manjarimeedeniya/Team_Morpheus/Enclosure Files/Photos/Bottom_2 from SolidWorks.png

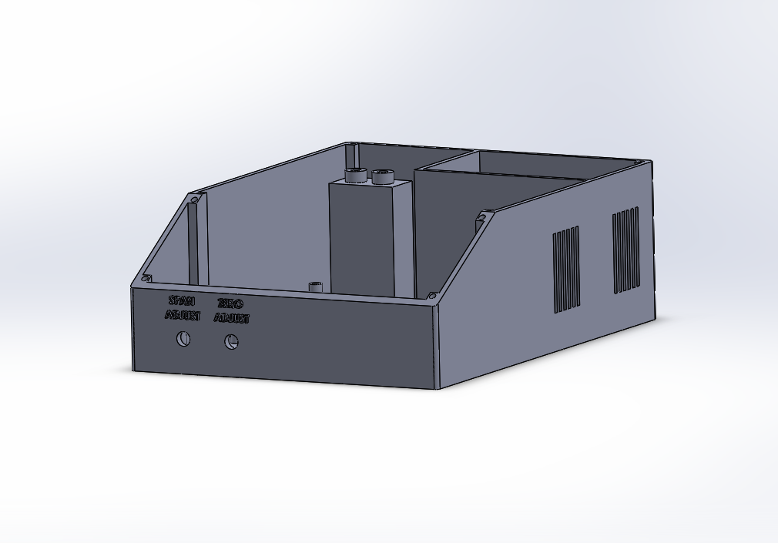
Enclosure Files/Photos/Bottom_2 from SolidWorks.png
