manjarimeedeniya/Team_Morpheus/Enclosure Files/Photos/Bottom_3 from SolidWorks.png

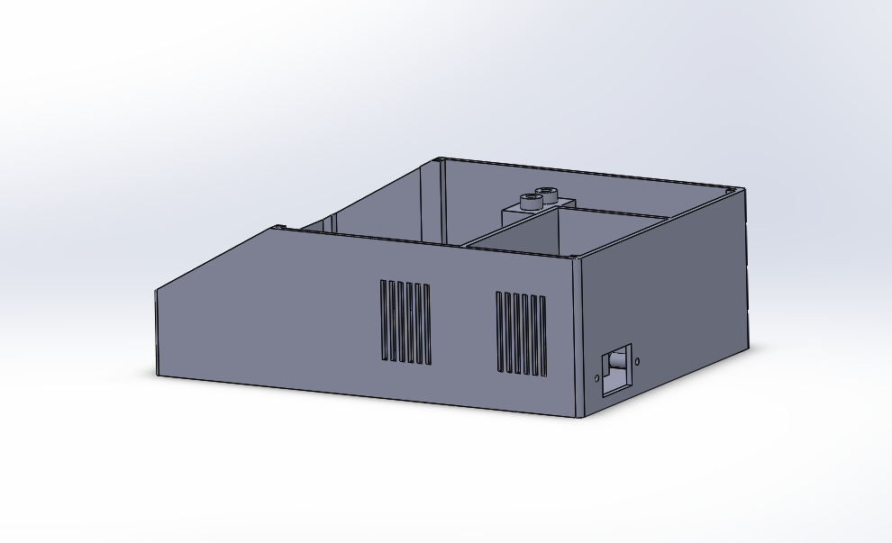
Enclosure Files/Photos/Bottom_3 from SolidWorks.png
