manjarimeedeniya/Team_Morpheus/Enclosure Files/Photos/Bottom_4 from SolidWorks.png

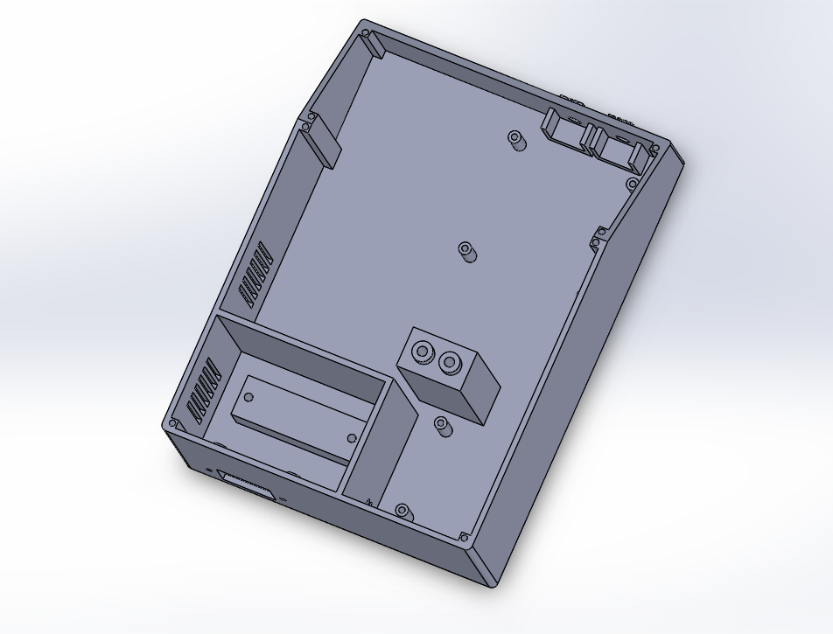
Enclosure Files/Photos/Bottom_4 from SolidWorks.png
