manjarimeedeniya/Team_Morpheus/Enclosure Files/Photos/FInal Enclosure from SolidWorks.png

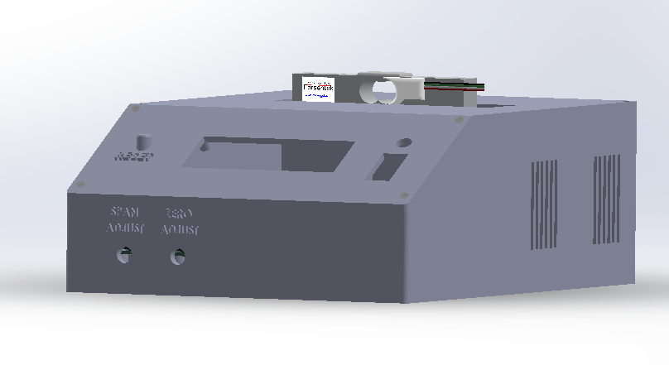
Enclosure Files/Photos/FInal Enclosure from SolidWorks.png
