manjarimeedeniya/Team_Morpheus/Enclosure Files/Photos/FInal Enclosure from SolidWorks_2.png

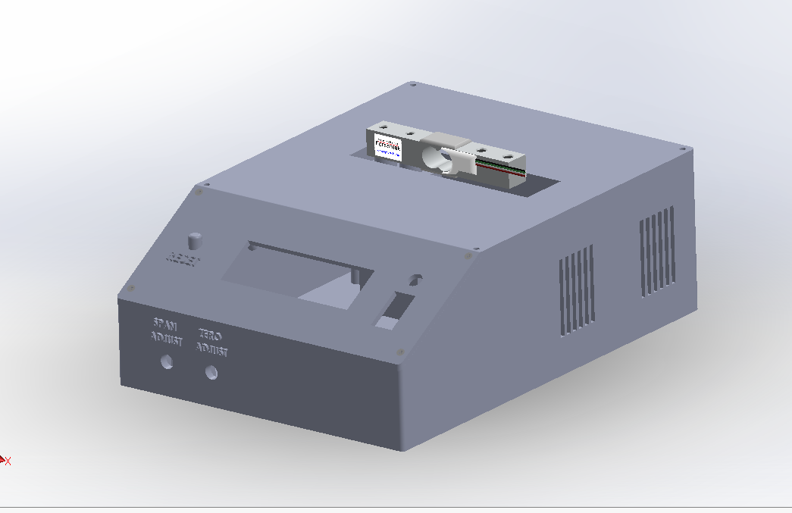
Enclosure Files/Photos/FInal Enclosure from SolidWorks_2.png
