manjarimeedeniya/Team_Morpheus/Enclosure Files/Photos/Top_1 from SolidWorks.png

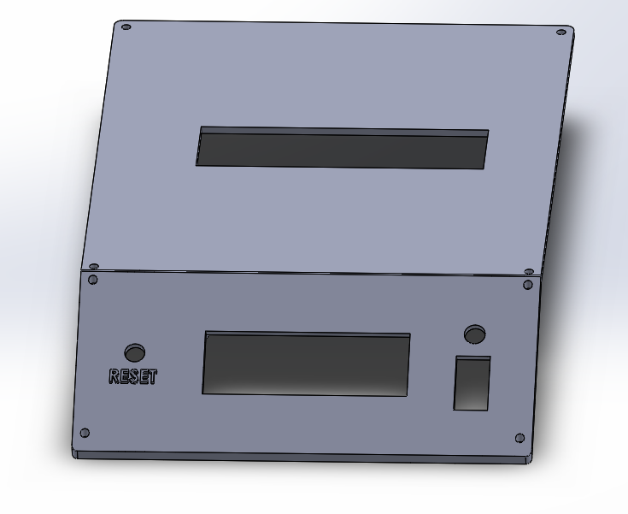
Enclosure Files/Photos/Top_1 from SolidWorks.png
