manjarimeedeniya/Team_Morpheus/Enclosure Files/Photos/Top_2 from SolidWorks.png

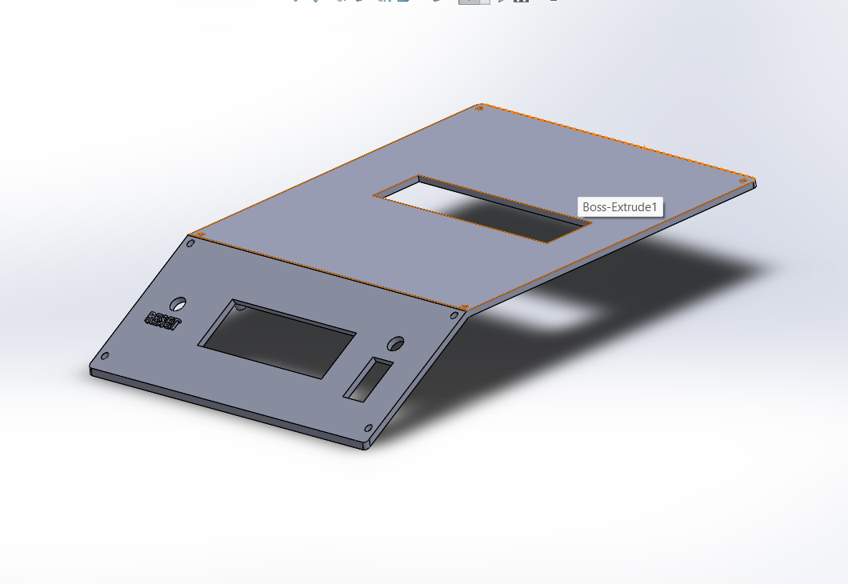
Enclosure Files/Photos/Top_2 from SolidWorks.png
