manjarimeedeniya/Team_Morpheus/Enclosure Files/Photos/Top_View from SolidWorks.png

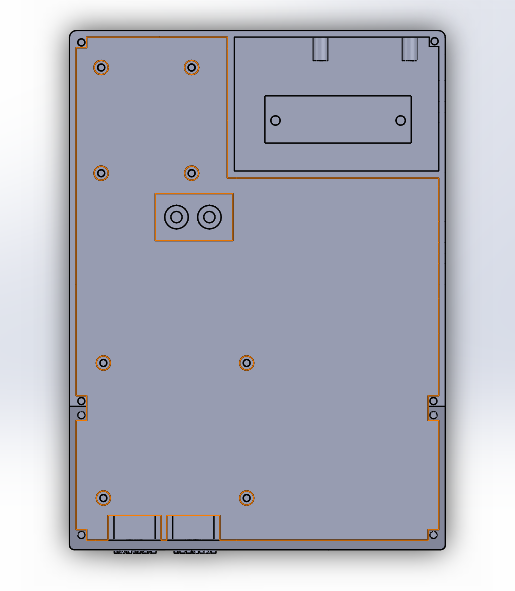
Enclosure Files/Photos/Top_View from SolidWorks.png
