manjarimeedeniya/Team_Morpheus/Final Product Photos/Final Product Photo 1.jpeg

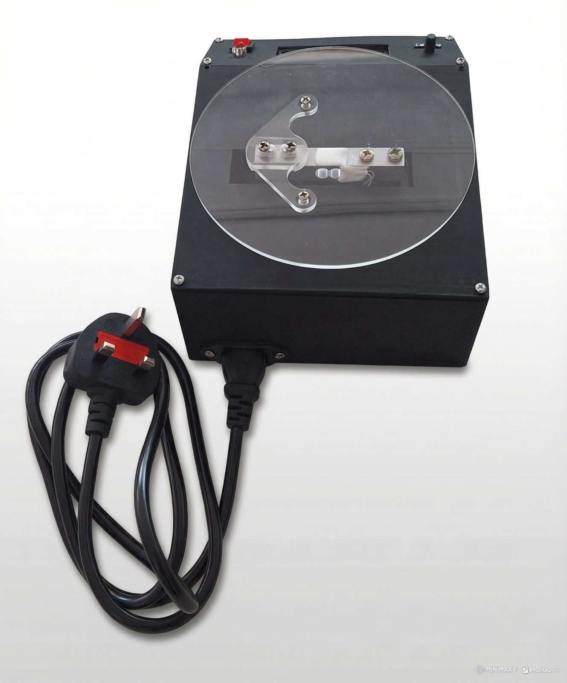
Final Product Photos/Final Product Photo 1.jpeg
