manjarimeedeniya/Team_Morpheus/Final Product Photos/Final Product Photo 3.jpeg

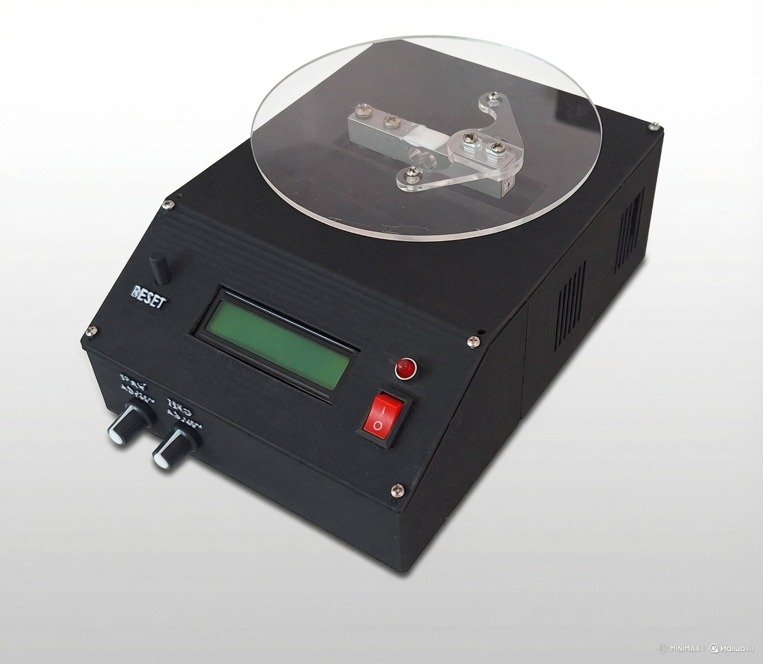
Final Product Photos/Final Product Photo 3.jpeg
