manjarimeedeniya/Team_Morpheus/Final Product Photos/Final Product Photo 4.jpeg

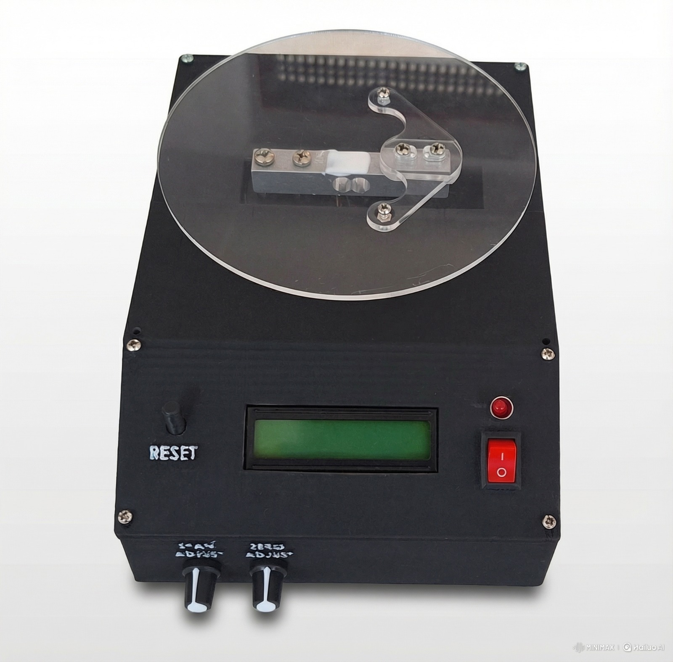
Final Product Photos/Final Product Photo 4.jpeg
