manjarimeedeniya/Team_Morpheus/Final Product Photos/Inside of the Final Product_1.jpeg

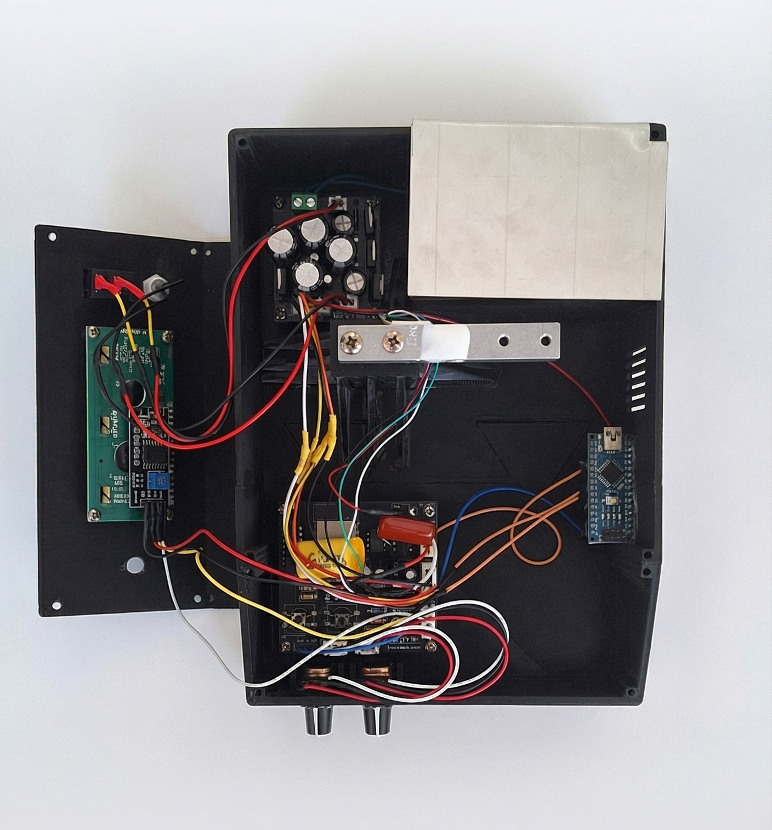
Final Product Photos/Inside of the Final Product_1.jpeg
