manjarimeedeniya/Team_Morpheus/Final Product Photos/Inside of the Final Product_2.jpeg

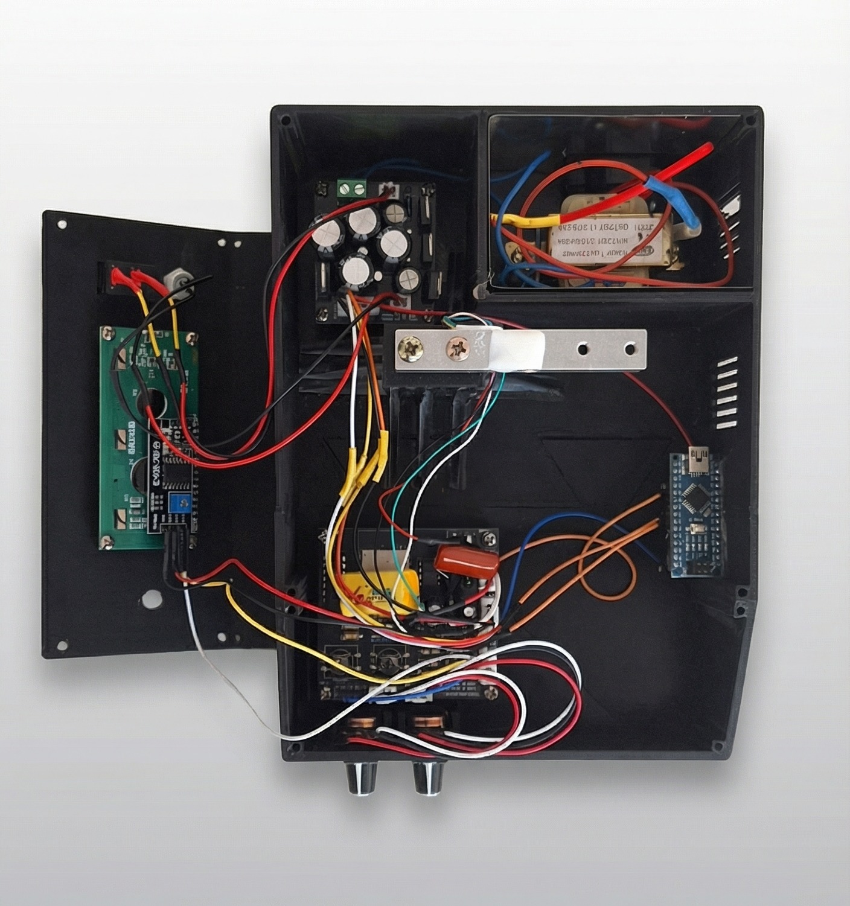
Final Product Photos/Inside of the Final Product_2.jpeg
