manjarimeedeniya/Team_Morpheus/PCB Files/Photos/Amplifier PCB 2D.png

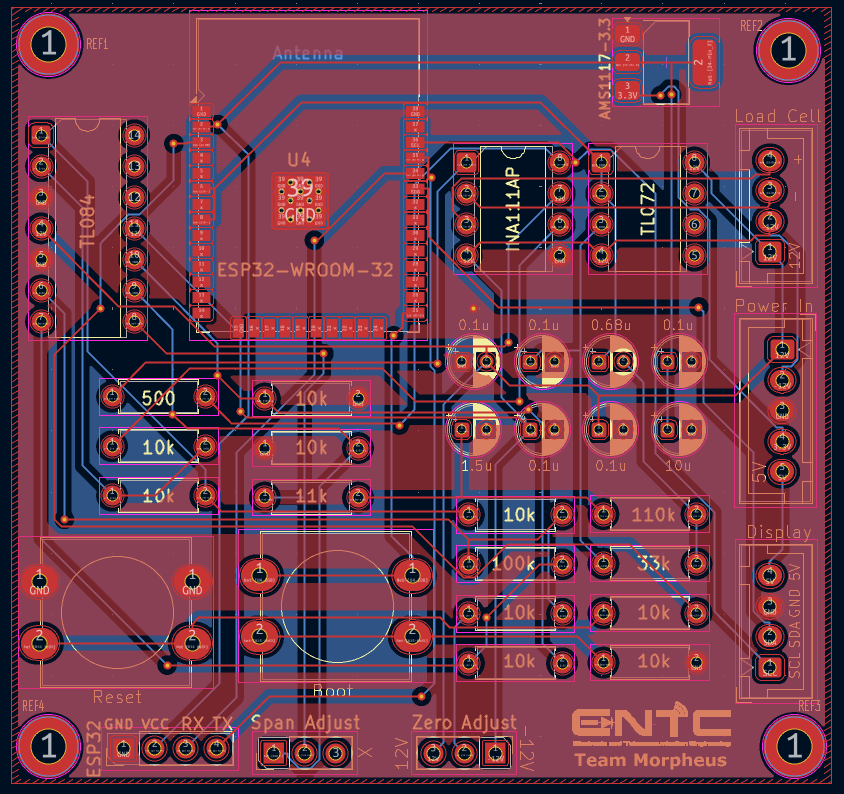
PCB Files/Photos/Amplifier PCB 2D.png
