manjarimeedeniya/Team_Morpheus/PCB Files/Photos/Power Supply PCB 3D.png

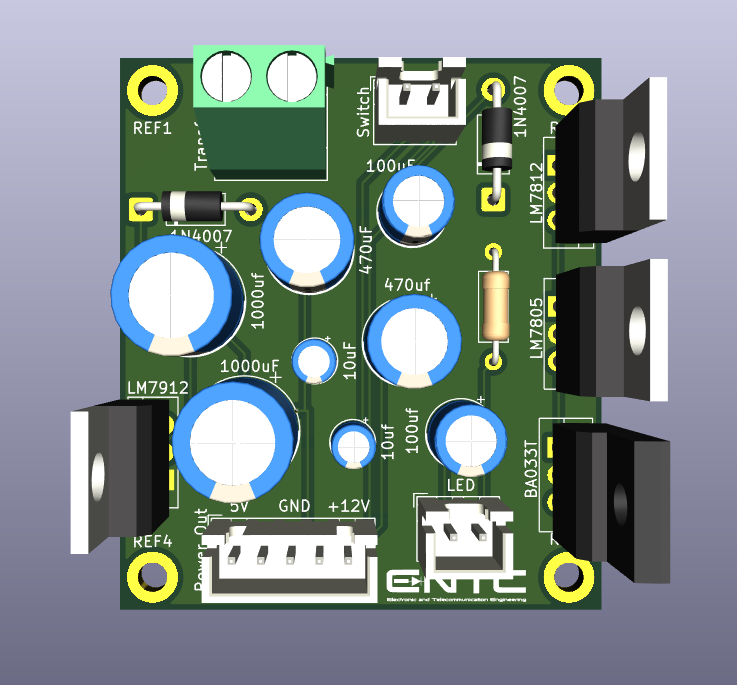
PCB Files/Photos/Power Supply PCB 3D.png
