manjarimeedeniya/Team_Morpheus/PCB Files/Photos/Power Supply PCB  2D.png

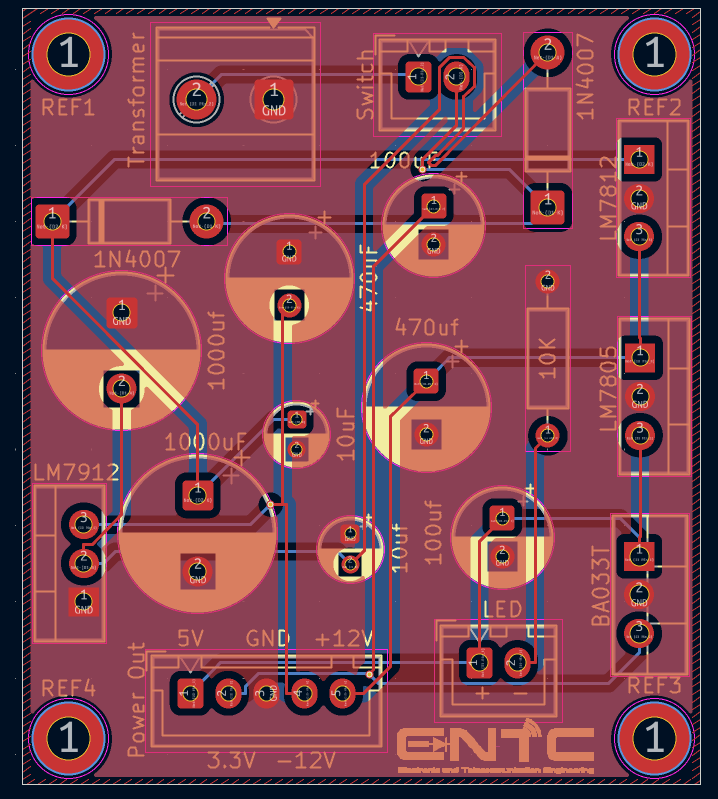
PCB Files/Photos/Power Supply PCB 2D.png
