manjarimeedeniya/Team_Morpheus/PCB Files/Photos/Power Supply PCB.jpeg

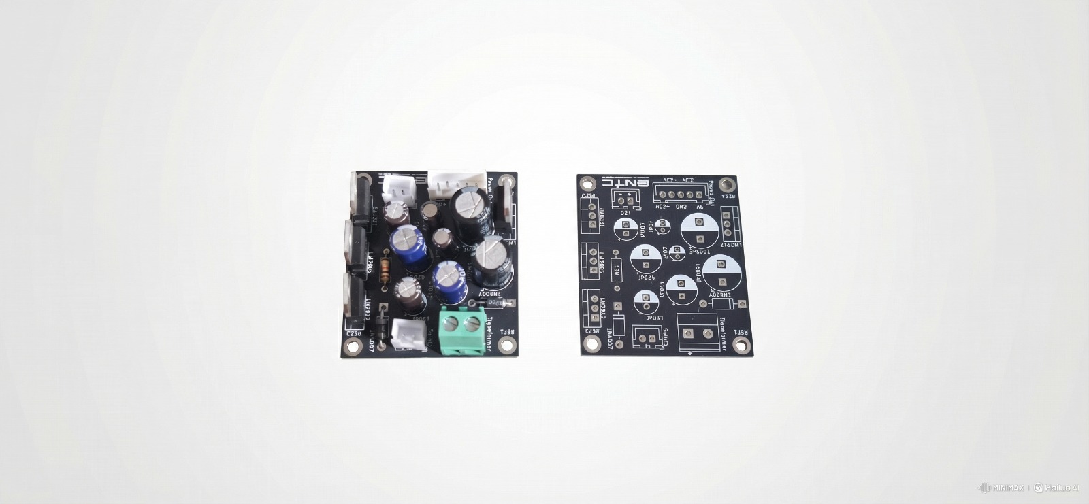
PCB Files/Photos/Power Supply PCB.jpeg
