manjarimeedeniya/Team_Morpheus/PCB Files/Photos/Soldered PCBs.jpeg

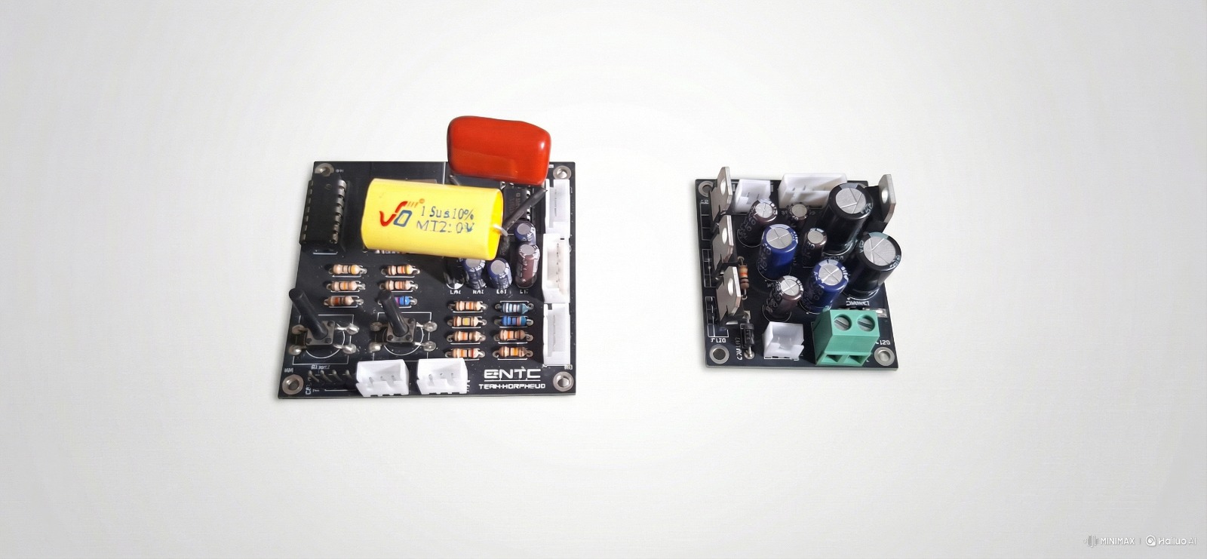
PCB Files/Photos/Soldered PCBs.jpeg
